grodansparadis/can4vscp_vilnius/docs/villnius_small.jpg

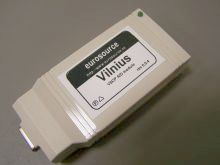
docs/villnius_small.jpg
