grodansparadis/can4vscp_vilnius/eagle/vilnius_brd_rev_B.png

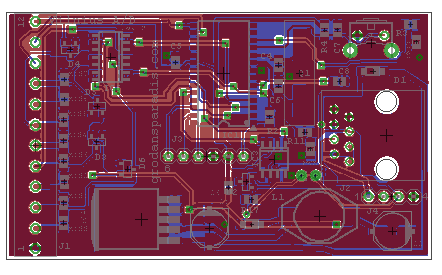
eagle/vilnius_brd_rev_B.png
