grodansparadis/can4vscp_vilnius/images/2015-12-04_13-33-04.png

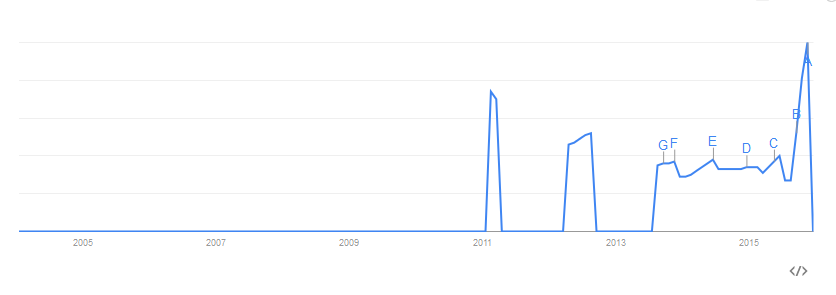
images/2015-12-04_13-33-04.png
