grodansparadis/can4vscp_vilnius/images/vilnius2.png

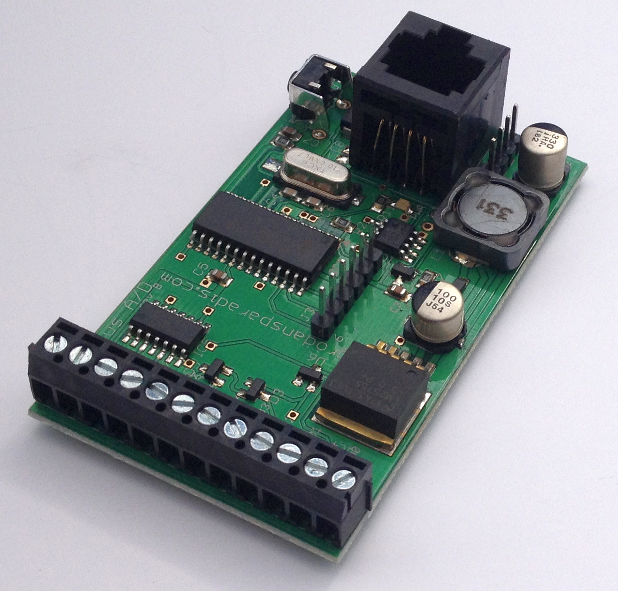
images/vilnius2.png
