grodansparadis/can4vscp_vilnius/images/vilnius4.png

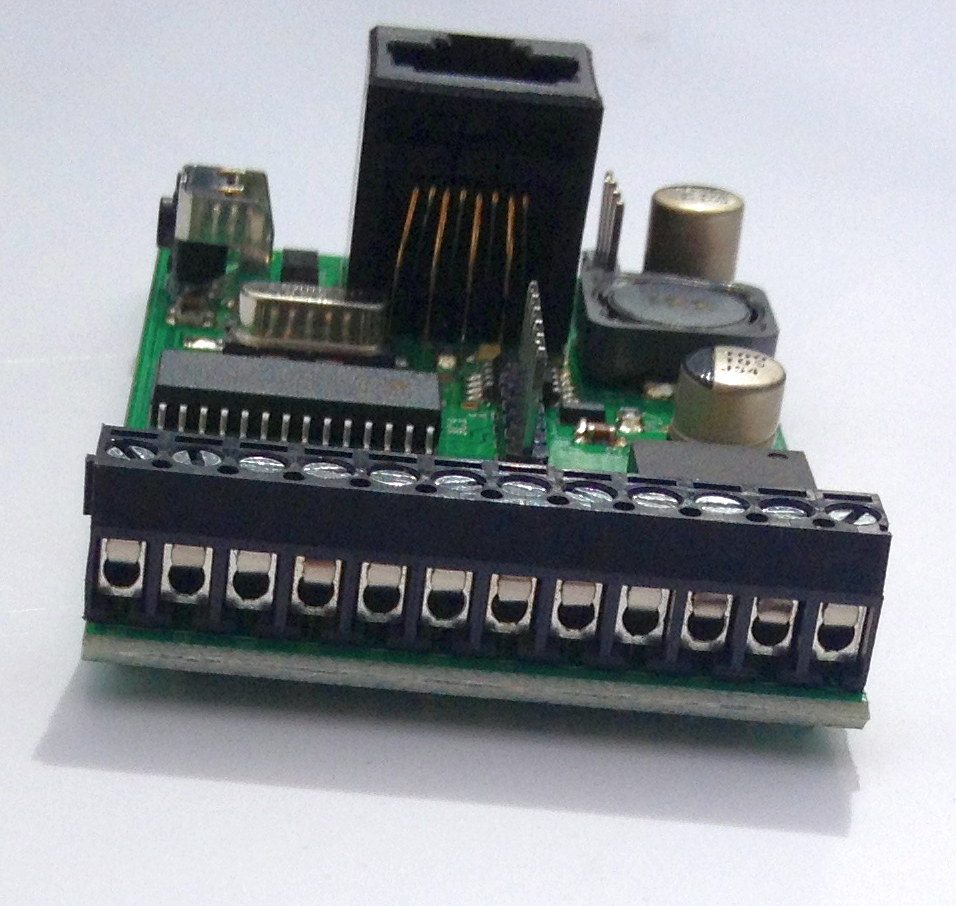
images/vilnius4.png
