grodansparadis/can4vscp_vilnius/images/vilnius6.png

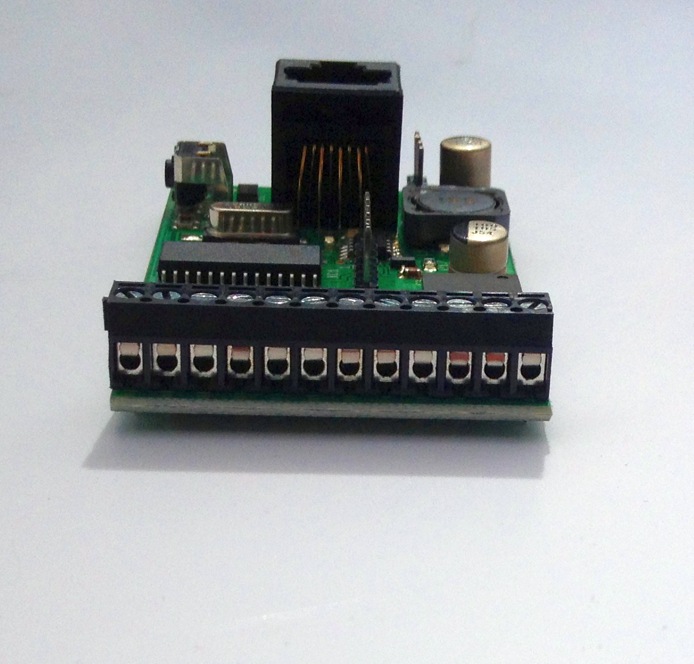
images/vilnius6.png
