grodansparadis/can4vscp_vilnius/images/vilnius7.png

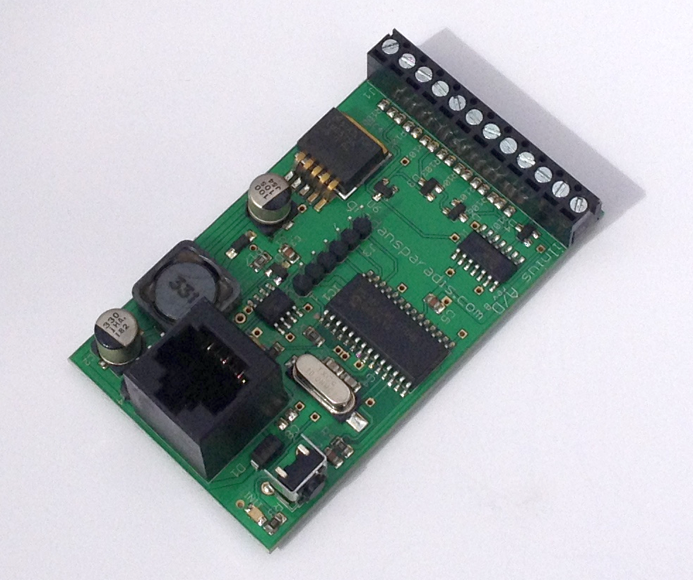
images/vilnius7.png
