grodansparadis/can4vscp_vilnius/images/vilnius8.png

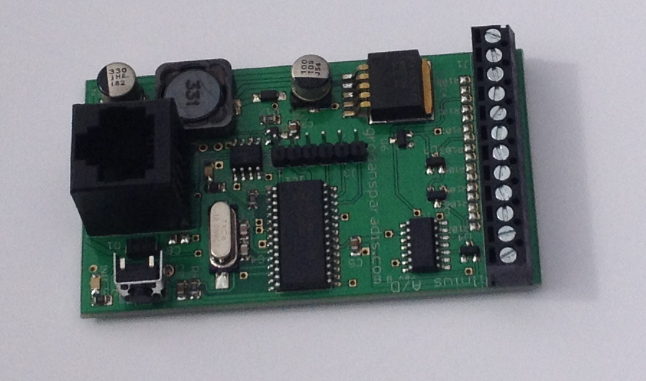
images/vilnius8.png
