grodansparadis/can4vscp_vilnius/images/vilnius9.png

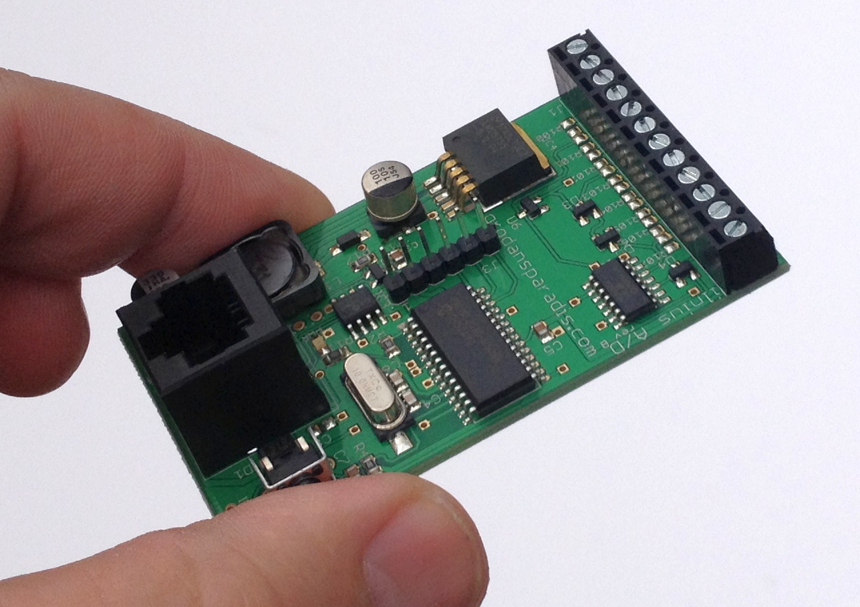
images/vilnius9.png
