grodansparadis/can4vscp_vilnius/images/vilnius10.png

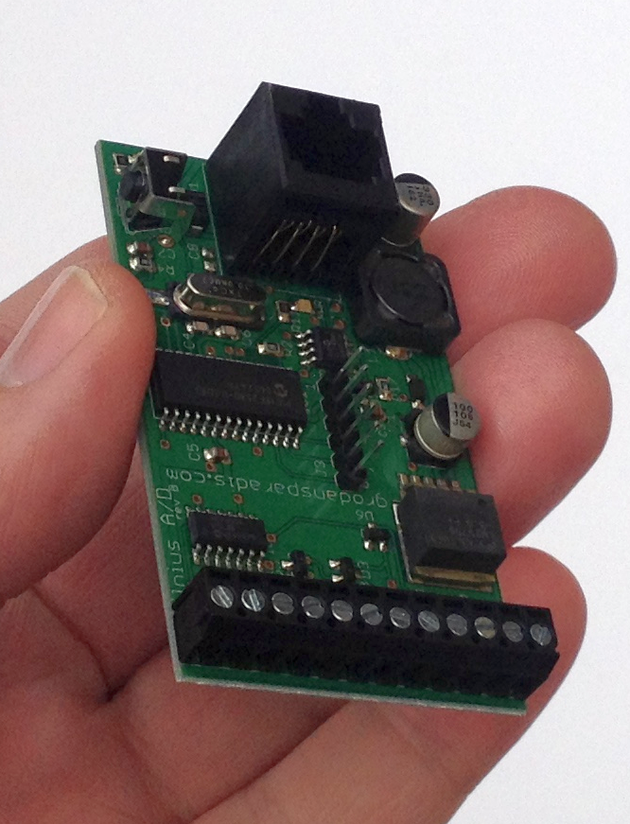
images/vilnius10.png
