grodansparadis/can4vscp_vilnius/images/vilnius11.png

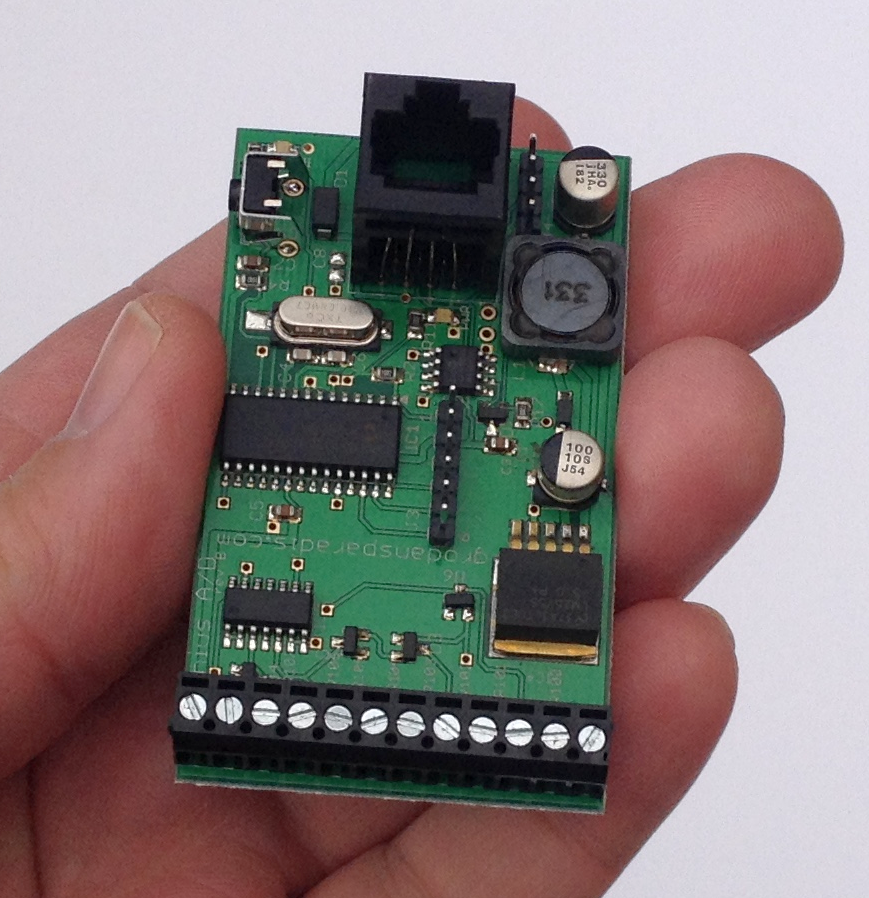
images/vilnius11.png
