grodansparadis/can4vscp_vilnius/images/vilnius12.png

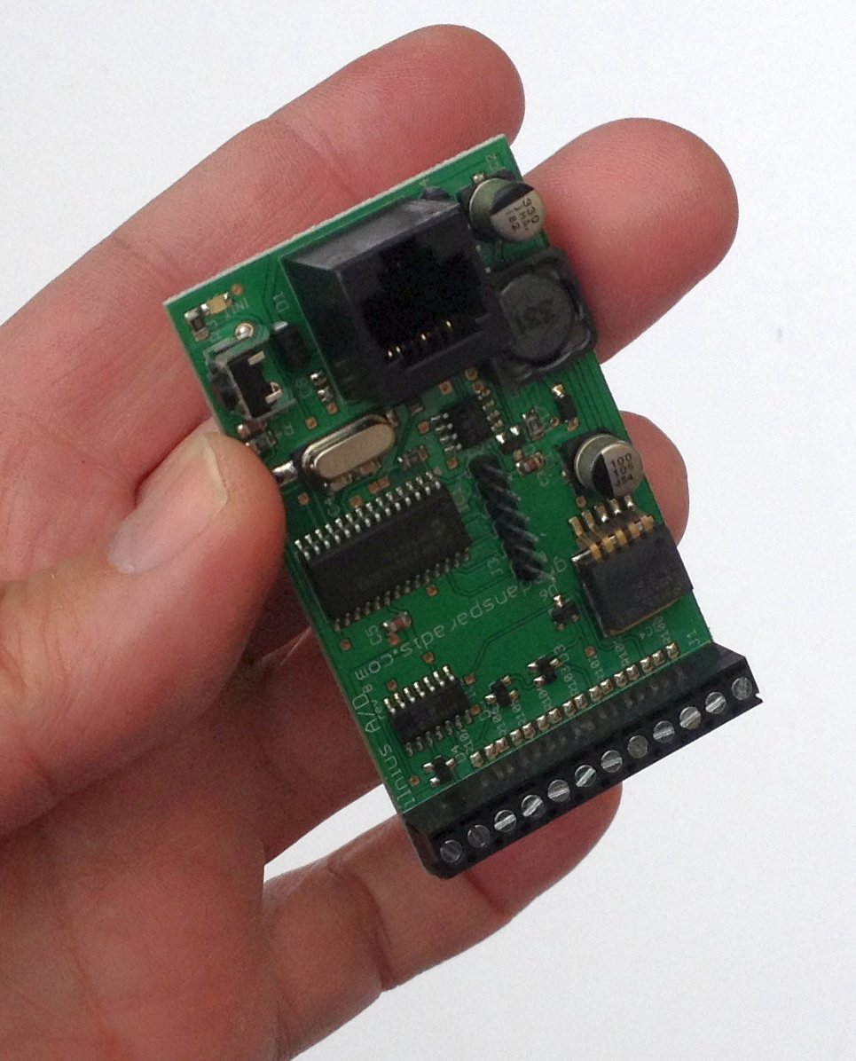
images/vilnius12.png
