grodansparadis/can4vscp_vilnius/images/vilnius14.png

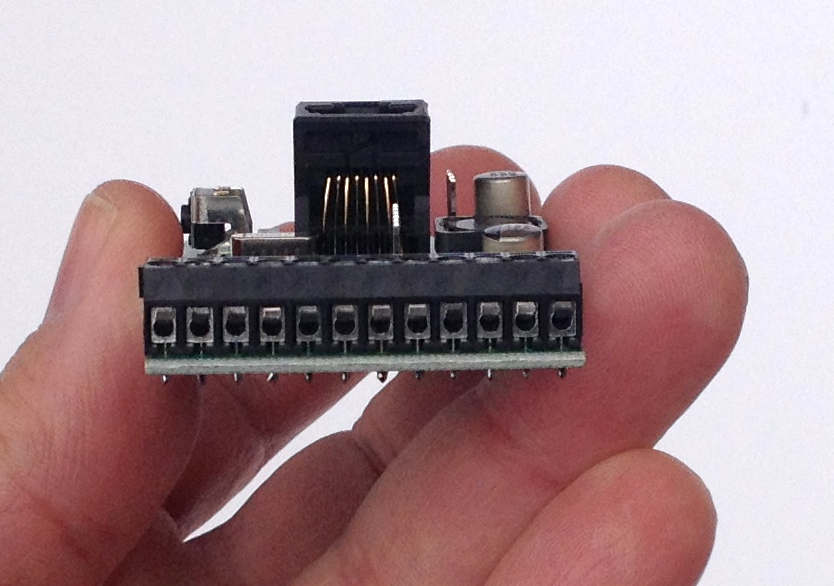
images/vilnius14.png
