grodansparadis/can4vscp_vilnius/images/vilnius15.png

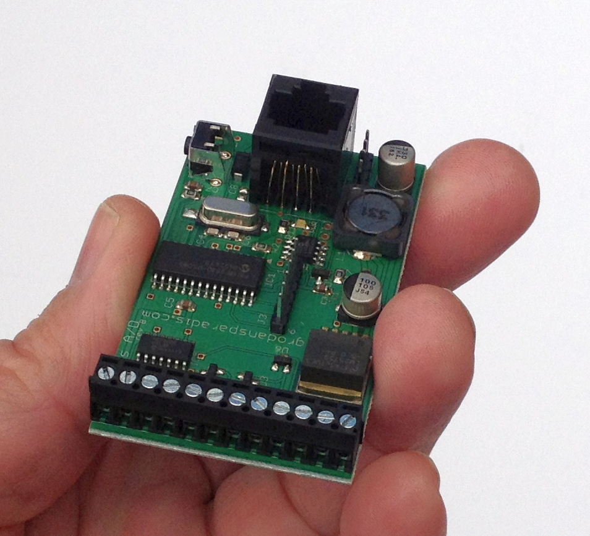
images/vilnius15.png
