grodansparadis/can4vscp_vilnius/images/vilnius16.png

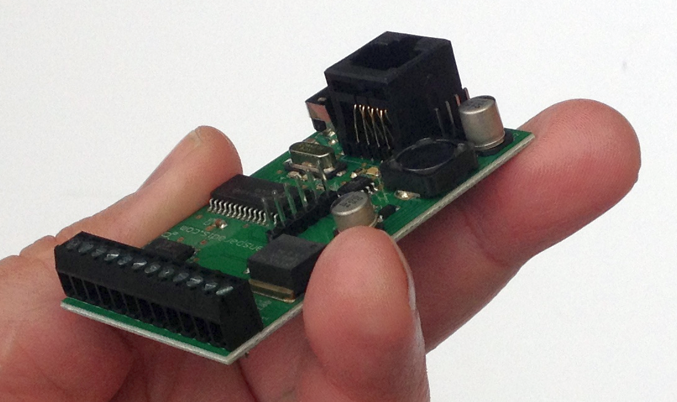
images/vilnius16.png
