grodansparadis/can4vscp_vilnius/images/vilnius.png

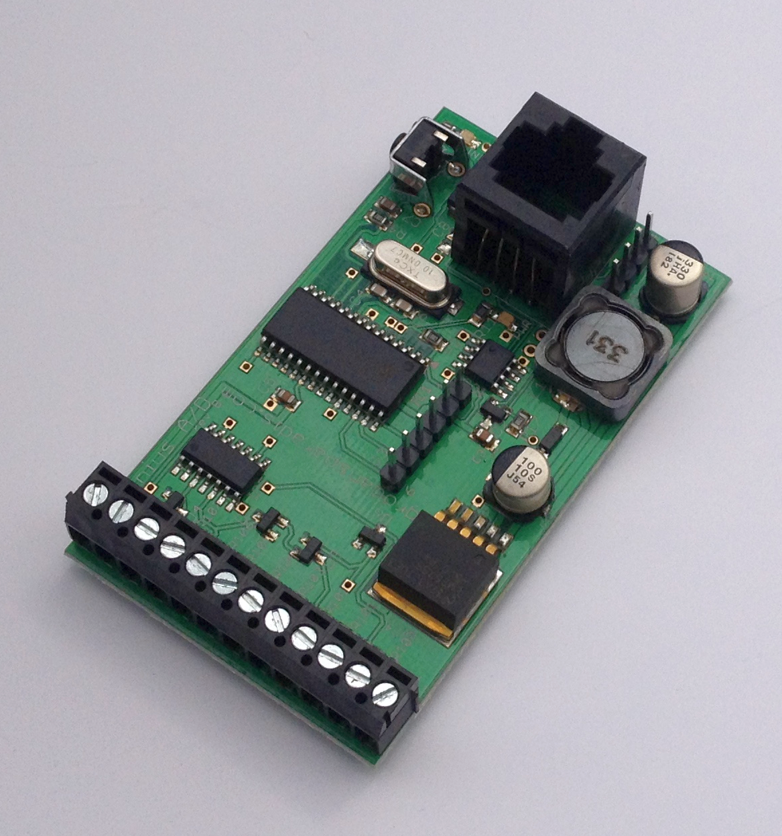
images/vilnius.png
