grodansparadis/can4vscp_vilnius/images/vilnius_sch1_rev_b.png

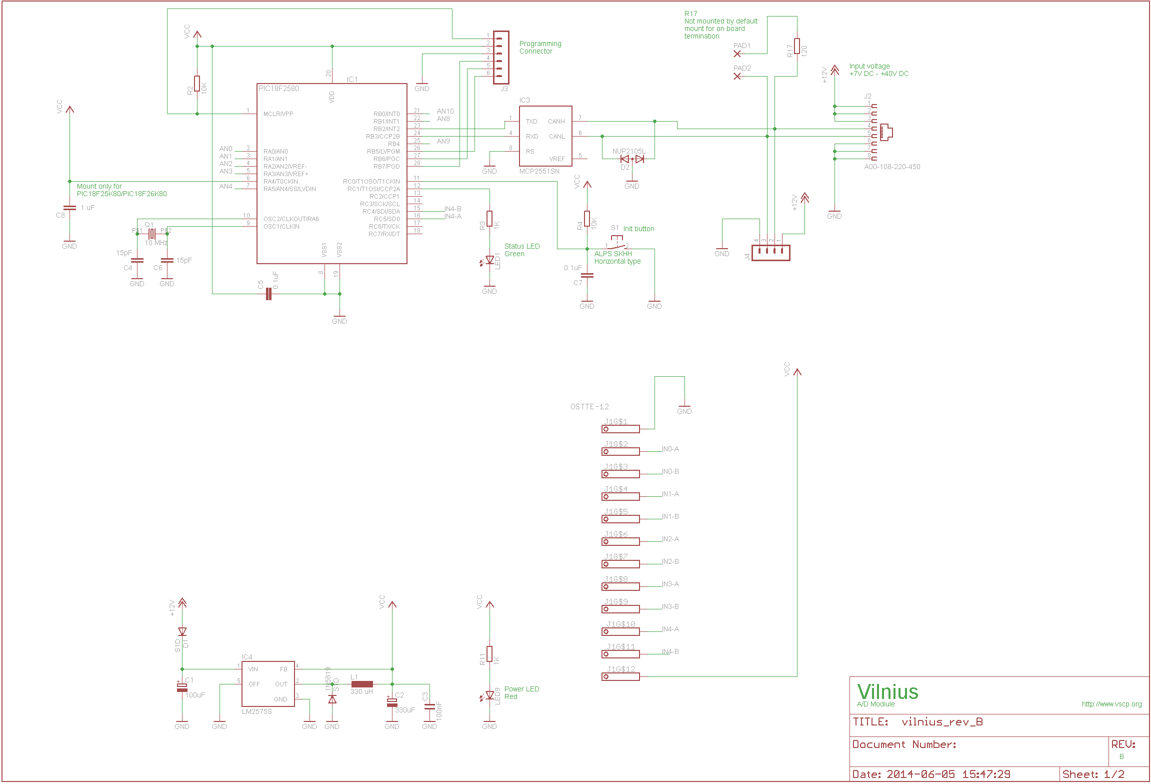
images/vilnius_sch1_rev_b.png
