grodansparadis/can4vscp_vilnius/images/vilnius_sch2_rev_b.png

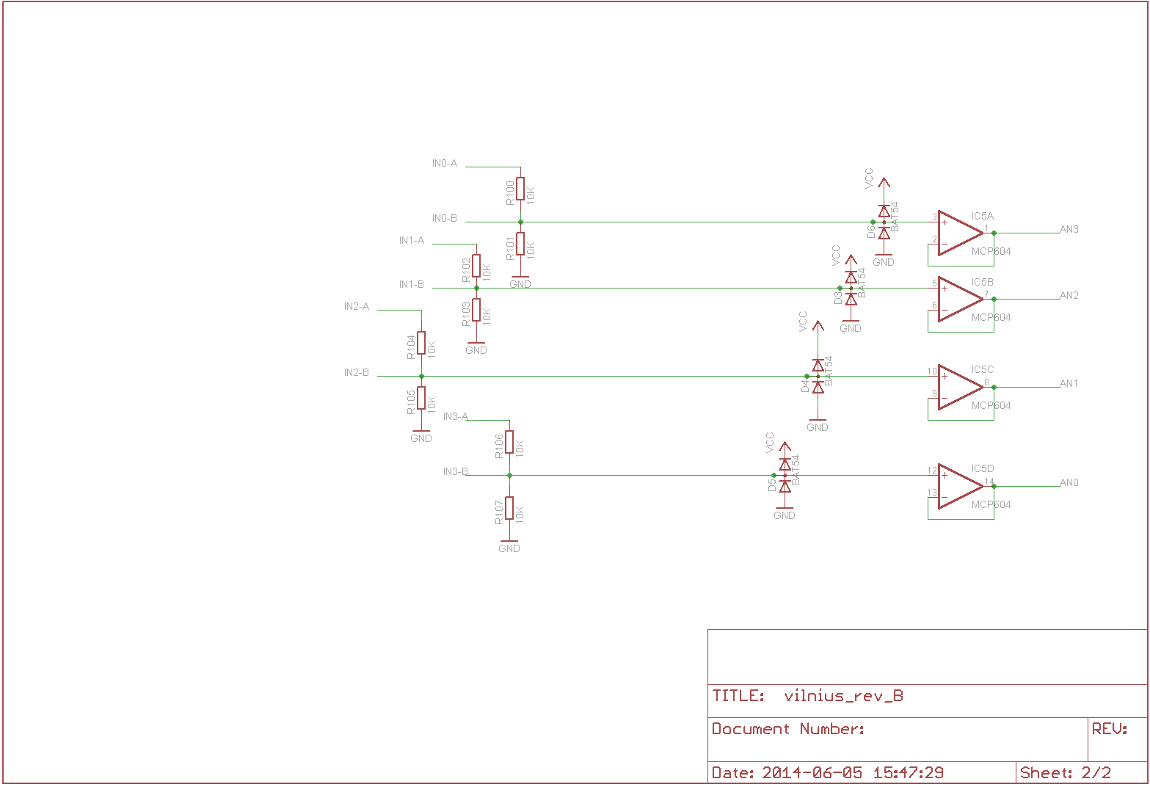
images/vilnius_sch2_rev_b.png
